terriblefire/tf1230/boards/tf330r1/tf330r1_main_top.v

`timescale 1ns / 1ps

/*
Copyright (c) 2018, Stephen J. Leary
All rights reserved.

Redistribution and use in source and binary forms, with or without
modification, are permitted provided that the following conditions are met:
1. Redistributions of source code must retain the above copyright
   notice, this list of conditions and the following disclaimer.
2. Redistributions in binary form must reproduce the above copyright
   notice, this list of conditions and the following disclaimer in the
   documentation and/or other materials provided with the distribution.
3. All advertising materials mentioning features or use of this software
   must display the following acknowledgement:
   This product includes software developed by the <organization>.
4. Neither the name of the <organization> nor the
   names of its contributors may be used to endorse or promote products
   derived from this software without specific prior written permission.

THIS SOFTWARE IS PROVIDED BY <COPYRIGHT HOLDER> ''AS IS'' AND ANY
EXPRESS OR IMPLIED WARRANTIES, INCLUDING, BUT NOT LIMITED TO, THE IMPLIED
WARRANTIES OF MERCHANTABILITY AND FITNESS FOR A PARTICULAR PURPOSE ARE
DISCLAIMED. IN NO EVENT SHALL <COPYRIGHT HOLDER> BE LIABLE FOR ANY
DIRECT, INDIRECT, INCIDENTAL, SPECIAL, EXEMPLARY, OR CONSEQUENTIAL DAMAGES
(INCLUDING, BUT NOT LIMITED TO, PROCUREMENT OF SUBSTITUTE GOODS OR SERVICES;
LOSS OF USE, DATA, OR PROFITS; OR BUSINESS INTERRUPTION) HOWEVER CAUSED AND
ON ANY THEORY OF LIABILITY, WHETHER IN CONTRACT, STRICT LIABILITY, OR TORT
(INCLUDING NEGLIGENCE OR OTHERWISE) ARISING IN ANY WAY OUT OF THE USE OF THIS
SOFTWARE, EVEN IF ADVISED OF THE POSSIBILITY OF SUCH DAMAGE.

*/

module tf330r1_main_top(

           inout			RESET,
           inout  			HALT,

           // all clock lines.
           inout   			CLK14M,
           inout   			CLK100M,
           inout   		CLKCPU,
           inout  			CLKRAM,

           inout [31:0]    	A,
           inout [31:24]   	D,

           //  SDRAM Control
           inout			CLKRAME,
           inout [12:0]    ARAM,
           inout [1:0] 	BA,
           inout			CAS,
           inout [3:0] 	DQM,
           inout			RAMWE,
           inout			RAS,
           inout			RAMCS,
           inout			RAMOE,

           // transfer control lines
           inout [1:0] 		SIZ,
           inout [2:0] 		FC,
           inout[2:0] 		IPL,

           // cache control lines.
           inout			CBREQ,
           inout			CBACK,
           inout			CIIN,

           // 68030 control lines
           inout			AS30,
           inout			DS30,
           inout			RW30,

           inout [1:0] 	DS30ACK,
           inout			STERM,

           inout			BGACK30,
           inout			BR30,
           inout			BG30,

           // CD32 / 68020 control lines
           inout			AS20,
           inout			DS20,
           inout			RW20,

           inout			BR20,
           inout			BG20,
           inout			BGACK20,

           inout [1:0] 		DSACK,

           inout			IOW,
           inout           IOR,

           inout			IDEINT,
           inout			IDEWAIT,
           inout [1:0] 	IDECS,
           inout			PUNT,
           inout			BERR,

           inout            EXP_BR,
           inout           EXP_BG,

           inout			INT2,
           inout			IDELED,
           inout			ACTIVE,

           inout			RXD,
           inout			RXD_EXT,

           inout			TXD,
           inout			TXD_EXT
       );

	// Instantiate the module
	main_top MAIN (
		.RESET(RESET),
        .DISABLE(1'b0), 
		.HALT(HALT), 
		.CLK14M(CLK14M), 
		.CLK100M(CLK100M), 
		.CLKCPU(CLKCPU), 
		.CLKRAM(CLKRAM), 
		.A(A), 
		.D(D), 
		.CLKRAME(CLKRAME), 
		.ARAM(ARAM), 
		.BA(BA), 
		.CAS(CAS), 
		.DQM(DQM), 
		.RAMWE(RAMWE), 
		.RAS(RAS), 
		.RAMCS(RAMCS), 
		.RAMOE(RAMOE), 
		.SIZ(SIZ), 
		.FC(FC), 
		.IPL(IPL), 
		.CBREQ(CBREQ), 
		.CBACK(CBACK), 
		.CIIN(CIIN), 
		.AS30(AS30), 
		.DS30(DS30), 
		.RW30(RW30), 
		.DS30ACK(DS30ACK), 
		.STERM(STERM), 
		.BGACK30(BGACK30), 
		.BR30(BR30), 
		.BG30(BG30), 
		.AS20(AS20), 
		.DS20(DS20), 
		.RW20(RW20), 
		.BR20(BR20), 
		.BG20(BG20), 
		.BGACK20(BGACK20), 
		.DSACK(DSACK), 
		.IOW(IOW), 
		.IOR(IOR), 
		.IDEINT(IDEINT), 
		.IDEWAIT(IDEWAIT), 
		.IDECS(IDECS), 
		.PUNT(PUNT), 
		.BERR(BERR), 
		.EXP_BR(EXP_BR), 
		.EXP_BG(EXP_BG), 
		.INT2(INT2), 
		.IDELED(IDELED), 
		.ACTIVE(ACTIVE), 
		.RXD(RXD), 
		.RXD_EXT(RXD_EXT), 
		.TXD(TXD), 
		.TXD_EXT(TXD_EXT)
	);


endmodule
